Air-Calibre/Project-OAQ-Open-Air-Quality-Sampler/Media/Renders/Render (1).png

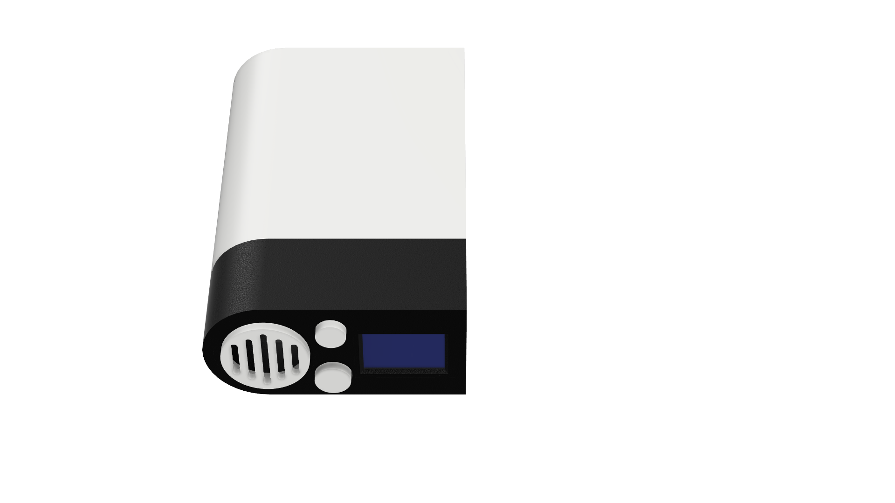
Media/Renders/Render (1).png
