Air-Calibre/Project-OAQ-Open-Air-Quality-Sampler/Media/Renders/Render (2).png

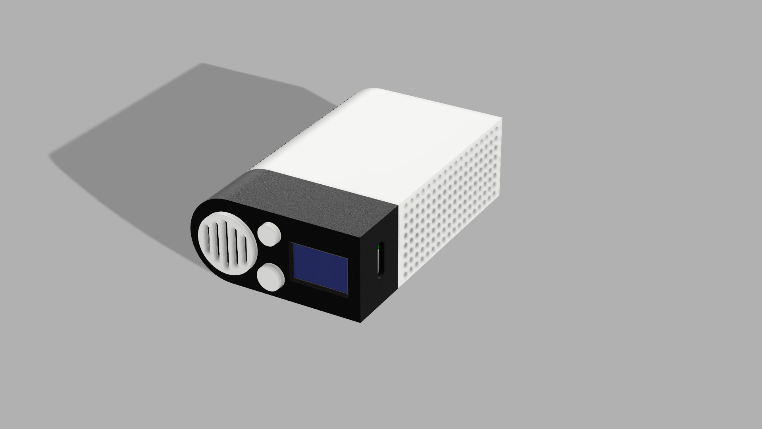
Media/Renders/Render (2).png
