Air-Calibre/Project-OAQ-Open-Air-Quality-Sampler/Media/Renders/Render (3).png

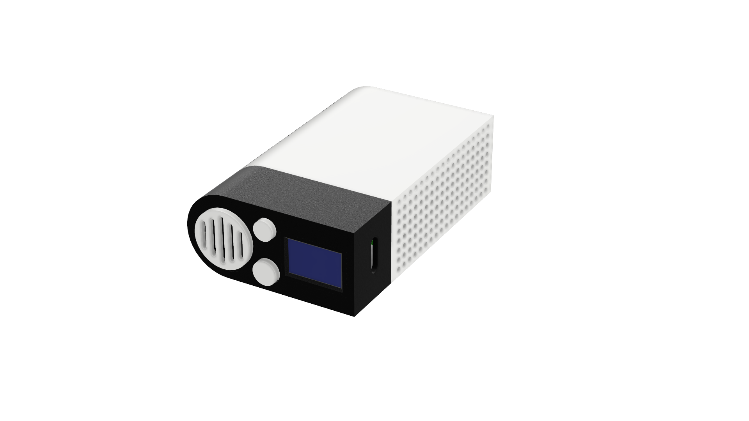
Media/Renders/Render (3).png
