Air-Calibre/Project-OAQ-Open-Air-Quality-Sampler/Media/Renders/Render (4).png

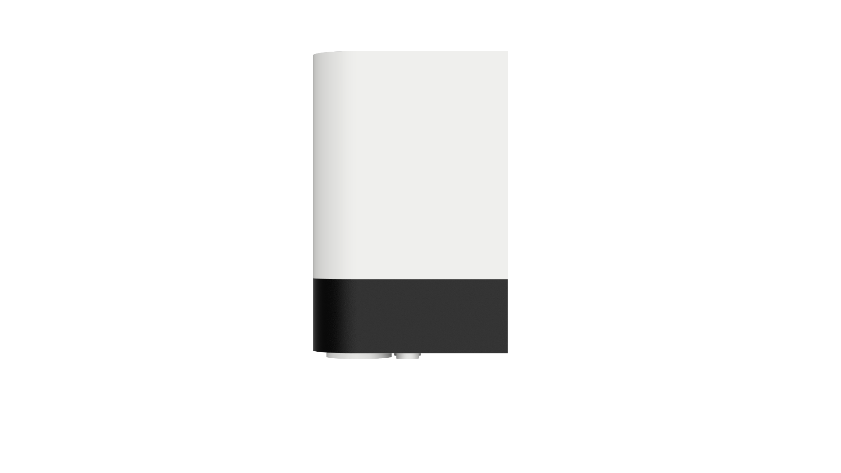
Media/Renders/Render (4).png
