Air-Calibre/Project-OAQ-Open-Air-Quality-Sampler/Media/Renders/Render (5).png

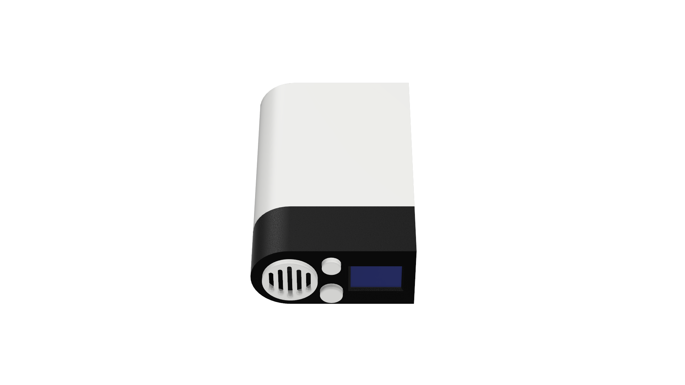
Media/Renders/Render (5).png
