Air-Calibre/Project-OAQ-Open-Air-Quality-Sampler/Media/Renders/Render (7).png

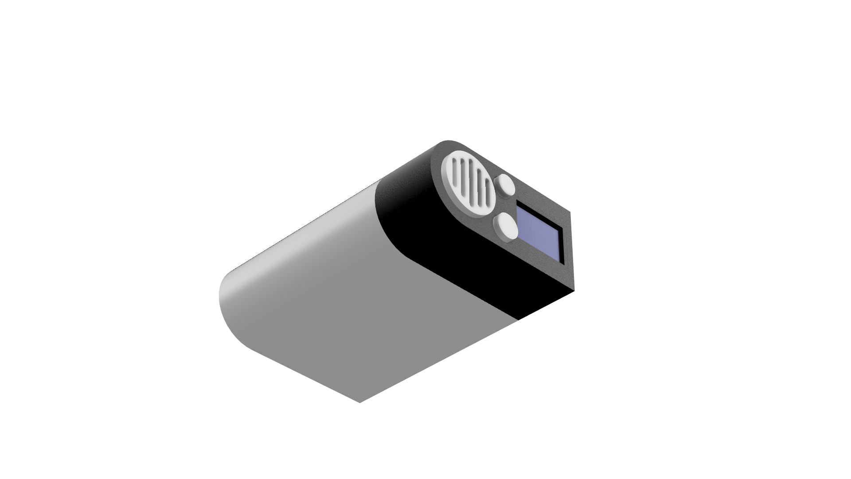
Media/Renders/Render (7).png
