Air-Calibre/Project-OAQ-Open-Air-Quality-Sampler/Media/Renders/Render (11).png

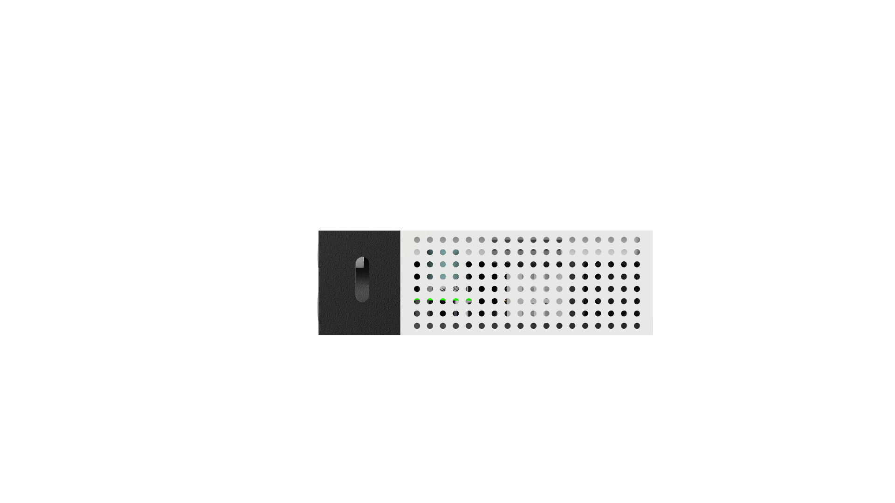
Media/Renders/Render (11).png
