Air-Calibre/Project-OAQ-Open-Air-Quality-Sampler/Media/Renders/Render (16).png

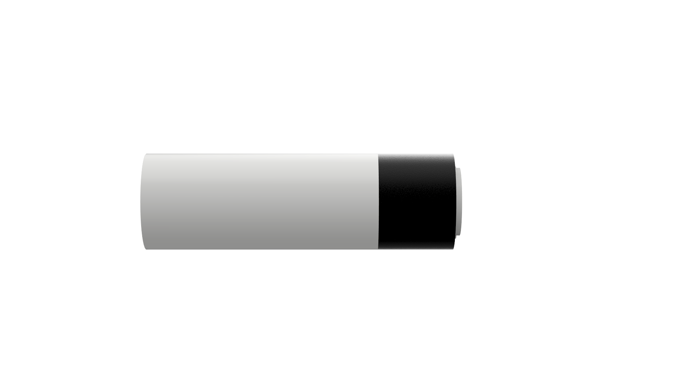
Media/Renders/Render (16).png
