Air-Calibre/Project-OAQ-Open-Air-Quality-Sampler/Media/Renders/Render (18).png

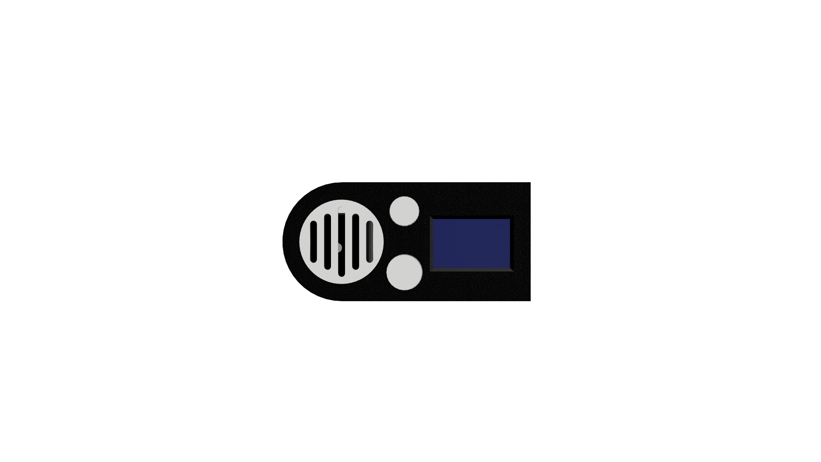
Media/Renders/Render (18).png
